reivaxy/aquaMonitor/hardware/case/20230510_080027.jpg

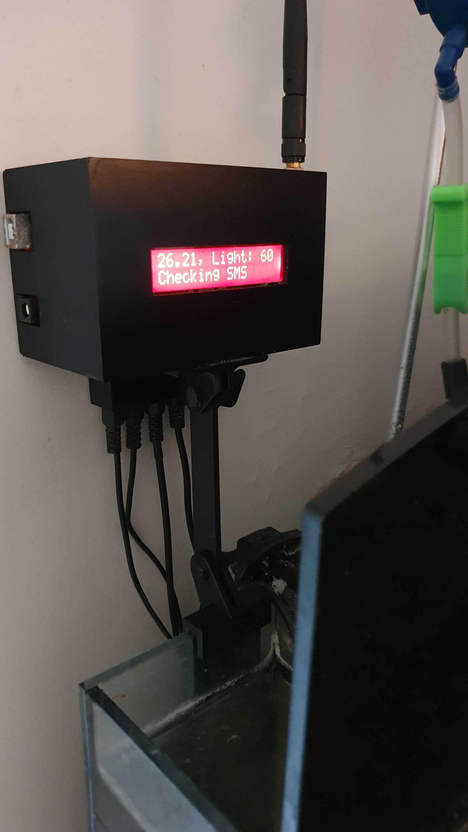
hardware/case/20230510_080027.jpg
