reivaxy/aquaMonitor/res/20160702_101324-1024.jpg

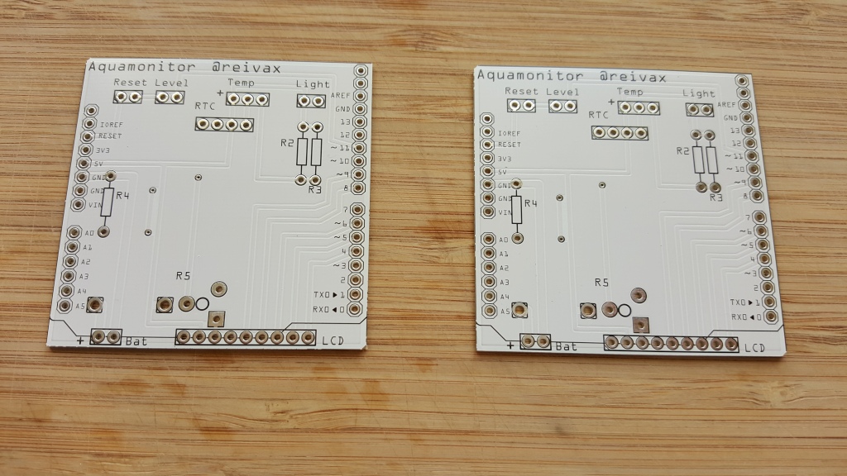
res/20160702_101324-1024.jpg
