reivaxy/aquaMonitor/res/20160702_121046-1024.jpg

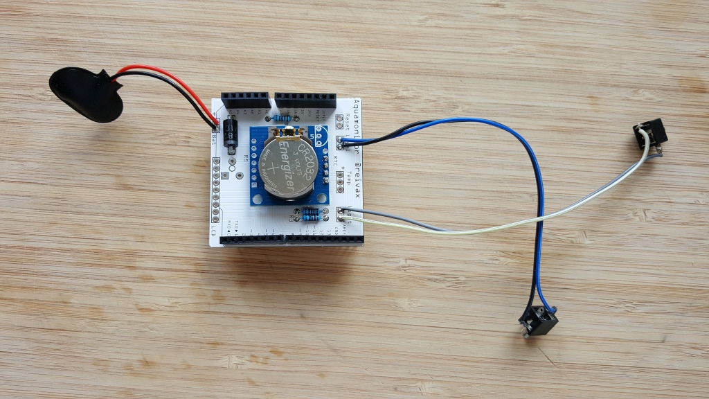
res/20160702_121046-1024.jpg
