reivaxy/aquaMonitor/res/20160702_131551-1024.jpg

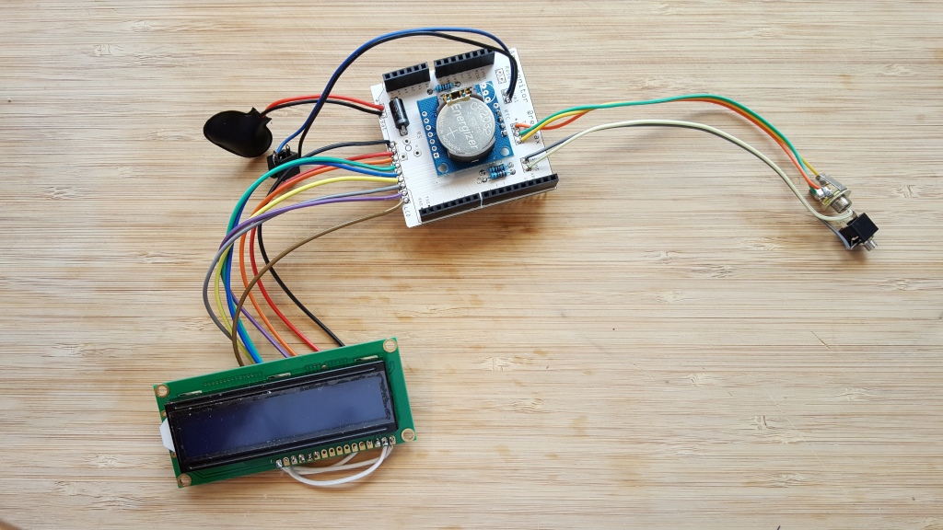
res/20160702_131551-1024.jpg
