reivaxy/aquaMonitor/res/20160702_132419-1024.jpg

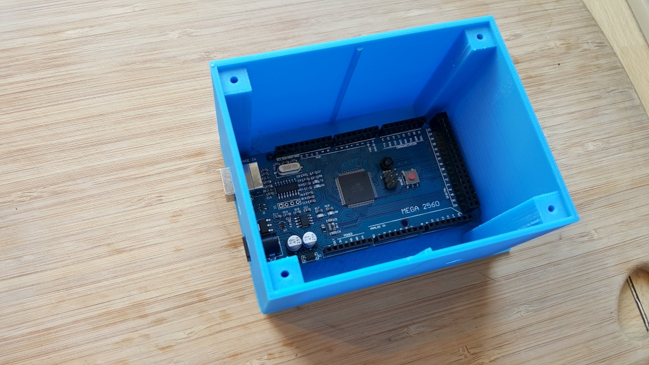
res/20160702_132419-1024.jpg
