reivaxy/aquaMonitor/res/20160702_132911-1024.jpg

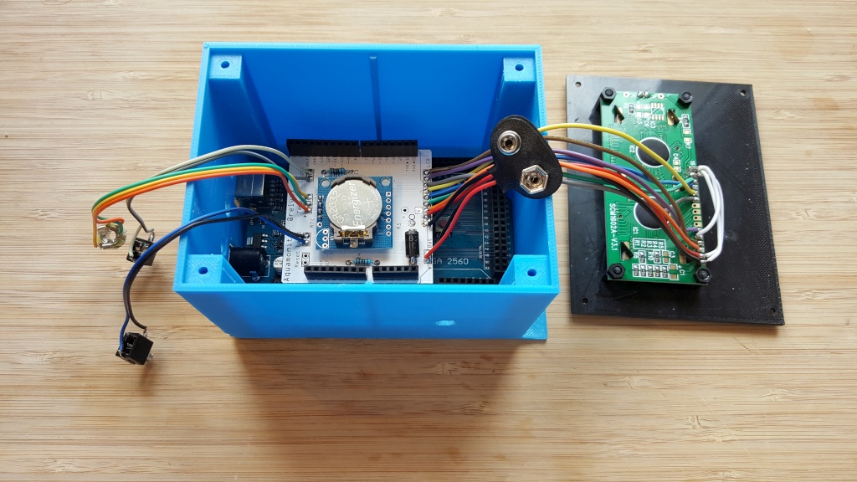
res/20160702_132911-1024.jpg
