reivaxy/aquaMonitor/res/20160702_133817-1024.jpg

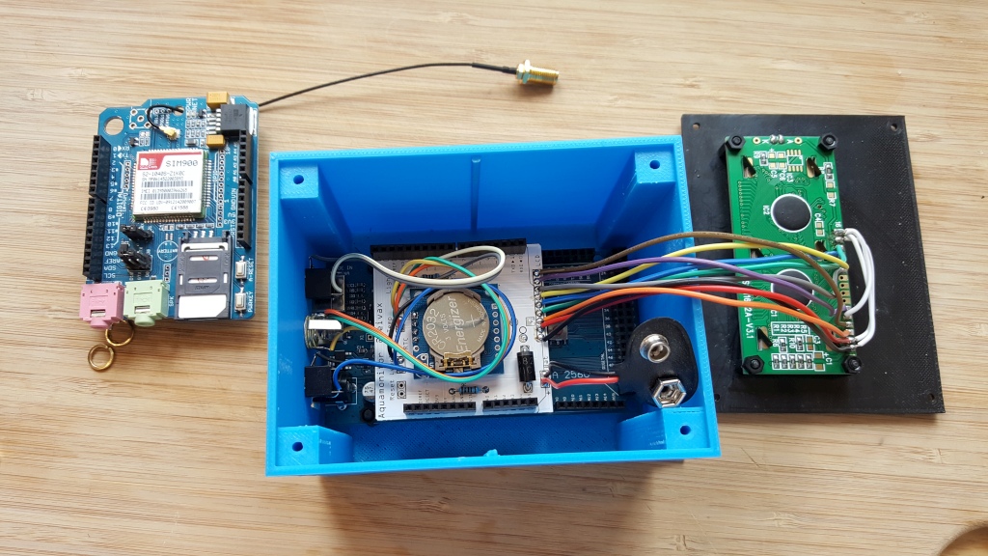
res/20160702_133817-1024.jpg
