reivaxy/aquaMonitor/res/20160702_134904-1024.jpg

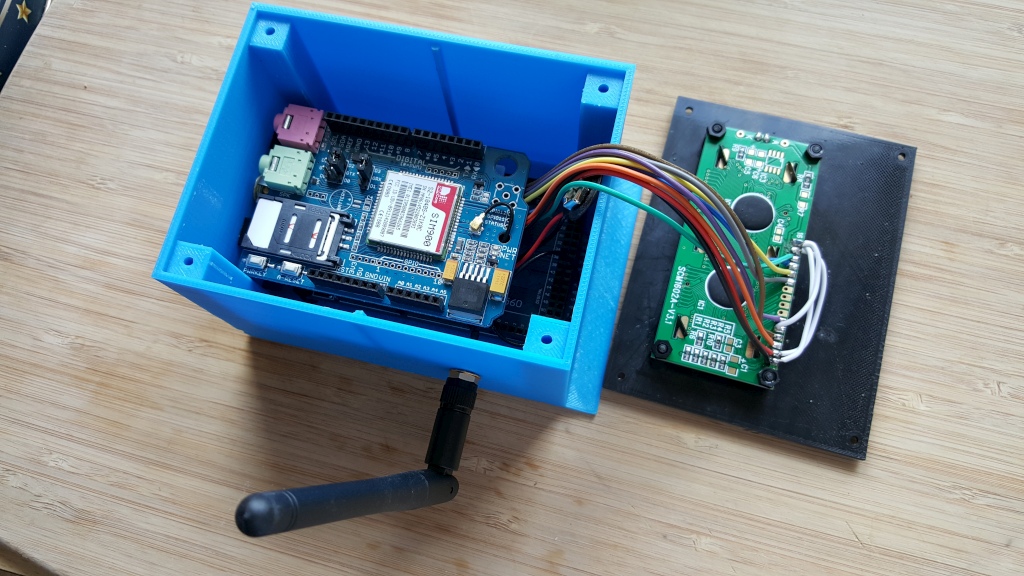
res/20160702_134904-1024.jpg
