reivaxy/aquaMonitor/res/20160702_145631-1024.jpg

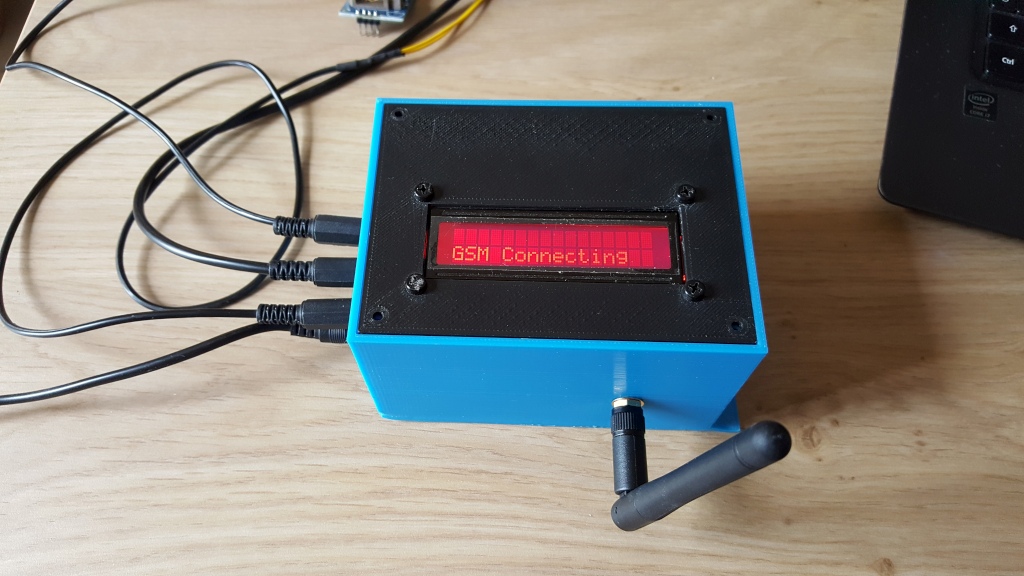
res/20160702_145631-1024.jpg
