reivaxy/aquaMonitor/res/powerDetection.jpg

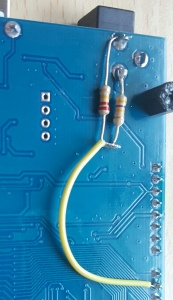
res/powerDetection.jpg
