reivaxy/aquaMonitor/res/sms1.png

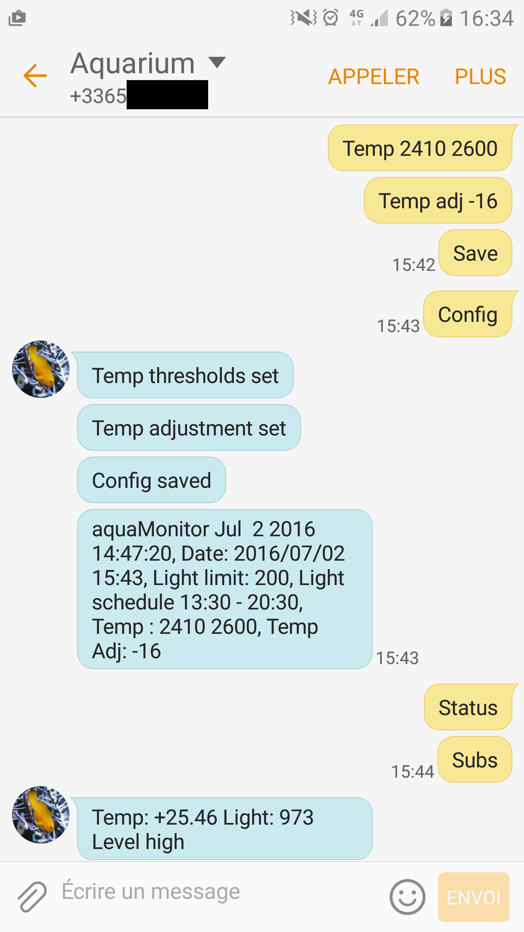
res/sms1.png
