reivaxy/aquaMonitor/aquaNet/aquaNetMessages.h

// Messages for aquaNet
// will be directed to arduino Serial (USB output) and LCD display
// They need to be kept short 
//
#define WIFI_CONFIG_INIT "Init wifi config"
#define WIFI_CONFIG_SAVING "Saving wifi config"
#define WIFI_CONFIG_SAVED "Saved wifi config"
#define CONNECTING_HOME_NETWORK "Connecting wifi"
#define CONNECTED_HOME_NETWORK "Connected %s"
#define CONNECTION_TIMED_OUT "Wifi time out"
#define ACCESS_IP "IP: "
#define CREATING_AP "Creating Access Point"
#define CLOSING_AP "Closing Access Point"
